shm-dmitry/xray-detector/xray-detector/display_st7735.cpp

#include "display_st7735.h"

#include "Arduino.h"
#include "clock.h"
#include "avr/pgmspace.h"

#define ST_CMD_DELAY 0x80 // special signifier for command lists

#define ST77XX_SWRESET 0x01
#define ST77XX_SLPOUT 0x11
#define ST77XX_MADCTL 0x36
#define ST77XX_INVOFF 0x20
#define ST77XX_COLMOD 0x3A
#define ST77XX_CASET 0x2A
#define ST77XX_RASET 0x2B
#define ST77XX_NORON 0x13
#define ST77XX_DISPON 0x29

#define ST7735_FRMCTR1 0xB1
#define ST7735_FRMCTR2 0xB2
#define ST7735_FRMCTR3 0xB3
#define ST7735_INVCTR 0xB4
#define ST7735_PWCTR1 0xC0
#define ST7735_PWCTR2 0xC1
#define ST7735_PWCTR3 0xC2
#define ST7735_PWCTR4 0xC3
#define ST7735_PWCTR5 0xC4
#define ST7735_VMCTR1 0xC5
#define ST7735_GMCTRP1 0xE0
#define ST7735_GMCTRN1 0xE1

#define ST77XX_MADCTL_MY 0x80
#define ST77XX_MADCTL_MX 0x40
#define ST77XX_MADCTL_MV 0x20
#define ST77XX_MADCTL_RGB 0x00

static const uint8_t PROGMEM DISPLAY_ST7335_COMMAND_LIST1[] = {                       // 7735R init, part 1 (red or green tab)
    15,                             // 15 commands in list:
    ST77XX_SWRESET,   ST_CMD_DELAY, //  1: Software reset, 0 args, w/delay
      150,                          //     150 ms delay
    ST77XX_SLPOUT,    ST_CMD_DELAY, //  2: Out of sleep mode, 0 args, w/delay
      255,                          //     500 ms delay
    ST7735_FRMCTR1, 3,              //  3: Framerate ctrl - normal mode, 3 arg:
      0x01, 0x2C, 0x2D,             //     Rate = fosc/(1x2+40) * (LINE+2C+2D)
    ST7735_FRMCTR2, 3,              //  4: Framerate ctrl - idle mode, 3 args:
      0x01, 0x2C, 0x2D,             //     Rate = fosc/(1x2+40) * (LINE+2C+2D)
    ST7735_FRMCTR3, 6,              //  5: Framerate - partial mode, 6 args:
      0x01, 0x2C, 0x2D,             //     Dot inversion mode
      0x01, 0x2C, 0x2D,             //     Line inversion mode
    ST7735_INVCTR,  1,              //  6: Display inversion ctrl, 1 arg:
      0x07,                         //     No inversion
    ST7735_PWCTR1,  3,              //  7: Power control, 3 args, no delay:
      0xA2,
      0x02,                         //     -4.6V
      0x84,                         //     AUTO mode
    ST7735_PWCTR2,  1,              //  8: Power control, 1 arg, no delay:
      0xC5,                         //     VGH25=2.4C VGSEL=-10 VGH=3 * AVDD
    ST7735_PWCTR3,  2,              //  9: Power control, 2 args, no delay:
      0x0A,                         //     Opamp current small
      0x00,                         //     Boost frequency
    ST7735_PWCTR4,  2,              // 10: Power control, 2 args, no delay:
      0x8A,                         //     BCLK/2,
      0x2A,                         //     opamp current small & medium low
    ST7735_PWCTR5,  2,              // 11: Power control, 2 args, no delay:
      0x8A, 0xEE,
    ST7735_VMCTR1,  1,              // 12: Power control, 1 arg, no delay:
      0x0E,
    ST77XX_INVOFF,  0,              // 13: Don't invert display, no args
    ST77XX_MADCTL,  1,              // 14: Mem access ctl (directions), 1 arg:
      0xC8,                         //     row/col addr, bottom-top refresh
    ST77XX_COLMOD,  1,              // 15: set color mode, 1 arg, no delay:
      0x05 };                       //     16-bit color

static const uint8_t PROGMEM DISPLAY_ST7335_COMMAND_LIST2[] = {                    // 7735R init, part 2 (red tab only)
    2,                              //  2 commands in list:
    ST77XX_CASET,   4,              //  1: Column addr set, 4 args, no delay:
      0x00, 0x00,                   //     XSTART = 0
      0x00, 0x7F,                   //     XEND = 127
    ST77XX_RASET,   4,              //  2: Row addr set, 4 args, no delay:
      0x00, 0x00,                   //     XSTART = 0
      0x00, 0x9F };

static const uint8_t PROGMEM DISPLAY_ST7335_COMMAND_LIST3[] = {                       // 7735R init, part 3 (red or green tab)
    4,                              //  4 commands in list:
    ST7735_GMCTRP1, 16      ,       //  1: Gamma Adjustments (pos. polarity), 16 args + delay:
      0x02, 0x1c, 0x07, 0x12,       //     (Not entirely necessary, but provides
      0x37, 0x32, 0x29, 0x2d,       //      accurate colors)
      0x29, 0x25, 0x2B, 0x39,
      0x00, 0x01, 0x03, 0x10,
    ST7735_GMCTRN1, 16      ,       //  2: Gamma Adjustments (neg. polarity), 16 args + delay:
      0x03, 0x1d, 0x07, 0x06,       //     (Not entirely necessary, but provides
      0x2E, 0x2C, 0x29, 0x2D,       //      accurate colors)
      0x2E, 0x2E, 0x37, 0x3F,
      0x00, 0x00, 0x02, 0x10,
    ST77XX_NORON,     ST_CMD_DELAY, //  3: Normal display on, no args, w/delay
      10,                           //     10 ms delay
    ST77XX_DISPON,    ST_CMD_DELAY, //  4: Main screen turn on, no args w/delay
      100 };                        //     100 ms delay


void display_st7735_run_command_list(const uint8_t *addr);

void display_st7735_init(uint8_t dc) {
  display_spi_init(dc);

  display_st7735_run_command_list(DISPLAY_ST7335_COMMAND_LIST1);
  display_st7735_run_command_list(DISPLAY_ST7335_COMMAND_LIST2);
  display_st7735_run_command_list(DISPLAY_ST7335_COMMAND_LIST3);

  uint8_t madctl = 0xC0;
  display_spi_send_command(ST77XX_MADCTL, &madctl, 1);

  madctl = ST77XX_MADCTL_MX | ST77XX_MADCTL_MY | ST77XX_MADCTL_RGB;
  display_spi_send_command(ST77XX_MADCTL, &madctl, 1);

  madctl = ST77XX_MADCTL_MX | ST77XX_MADCTL_MV | ST77XX_MADCTL_RGB;
  display_spi_send_command(ST77XX_MADCTL, &madctl, 1);
}

void display_st7735_run_command_list(const uint8_t *addr) {

  uint8_t numCommands, cmd, numArgs;
  uint16_t ms;

  numCommands = pgm_read_byte(addr++); // Number of commands to follow
  while (numCommands--) {              // For each command...
    cmd = pgm_read_byte(addr++);       // Read command
    numArgs = pgm_read_byte(addr++);   // Number of args to follow
    ms = numArgs & ST_CMD_DELAY;       // If hibit set, delay follows args
    numArgs &= ~ST_CMD_DELAY;          // Mask out delay bit
    display_spi_send_command_pgm(cmd, addr, numArgs);
    addr += numArgs;

    if (ms) {
      ms = pgm_read_byte(addr++); // Read post-command delay time (ms)
      if (ms == 255)
        ms = 500; // If 255, delay for 500 ms
      clock_delay(ms);
    }
  }
}
