shm-dmitry/xray-detector/xray-detector/gui_page_settings.cpp

#include "gui_page_settings.h"

#include "display.h"
#include "eeprom_control.h"
#include "uv_control.h"
#include "alarm_manager.h"
#include "gui_images.h"
#include "userinput.h"
#include "clock.h"
#include "rad_control.h"

#define SETTINGS_PAGE_UV_FREQ     0
#define SETTINGS_PAGE_UV_DUTY     1
#define SETTINGS_PAGE_UV_ON       2
#define SETTINGS_PAGE_DATE        3
#define SETTINGS_PAGE_TIME        4
#define SETTINGS_PAGE_IMPL2UR     5
#define SETTINGS_PAGE_ALARM_H     6
#define SETTINGS_PAGE_ALRM_L1     7
#define SETTINGS_PAGE_ALRM_L2     8
#define SETTINGS_PAGE_ALRM_NI     9
#define SETTINGS_PAGE_ALRM_OI     10

#define SETTINGS_PAGE_MINVAL  SETTINGS_PAGE_UV_FREQ
#define SETTINGS_PAGE_MAXVAL  SETTINGS_PAGE_ALRM_OI

#define SETTINGS_PAGE_UNCHANGED 0xFF

#define SETTINGS_PAGE_EDIT_DATETIME_UNCHANGED 0
#define SETTINGS_PAGE_EDIT_DATETIME_YEAR      1
#define SETTINGS_PAGE_EDIT_DATETIME_MONTH     2
#define SETTINGS_PAGE_EDIT_DATETIME_DAY       3
#define SETTINGS_PAGE_EDIT_DATETIME_HOUR      4
#define SETTINGS_PAGE_EDIT_DATETIME_MINUTE    5

#define SETTINGS_PAGE_Y_OFFSET 33

uint8_t menu_actual_prev   = SETTINGS_PAGE_MINVAL;
uint8_t menu_actual        = SETTINGS_PAGE_MINVAL;
uint8_t menu_change_value  = SETTINGS_PAGE_UNCHANGED;
bool menu_refreshed        = false;
uint8_t menu_edit_datetime = SETTINGS_PAGE_EDIT_DATETIME_UNCHANGED;

void gui_settings_page_print(uint8_t index, uint8_t value, const char * text);
void gui_settings_page_print_onoff(uint8_t index, bool value);
void gui_settings_page_print_date(uint8_t index);
void gui_settings_page_print_time(uint8_t index);
void gui_settings_page_print_alarm_onimpulse(uint8_t index);

bool gui_settings_page_refresh(uint8_t data) {
  if (!display_is_on()) {
    return false;
  }

  display_set_cursor(0, SETTINGS_PAGE_Y_OFFSET);
  display_set_textcolor(DISPLAY_WHITE);
  display_set_textsize(2);

  if (data) {
    if (data == USERINPUT_MOVE_LEFT) {
      menu_actual = SETTINGS_PAGE_MAXVAL;
    } else {
      menu_actual = SETTINGS_PAGE_MINVAL;
    }

    display_println("  UV freq: ");
    display_println("  UV freq: ");
    display_println("  UV: ");
    display_println("  Date: ");
    display_println("  Time: ");
    display_println("  Impl/uR: ");
    display_println(" Alarms:");
    display_println("  Level1: ");
    display_println("  Level2: ");
    display_println("  No Impuls: ");
    display_println("  On Each: ");
  }

  if (menu_actual_prev != menu_actual || data) {
    display_draw_bitmap(6, SETTINGS_PAGE_Y_OFFSET + 16 * menu_actual_prev + 5, IMG_ARROW, IMG_ARROW_W, IMG_ARROW_H, DISPLAY_BLACK);
    display_draw_bitmap(6, SETTINGS_PAGE_Y_OFFSET + 16 * menu_actual + 5, IMG_ARROW, IMG_ARROW_W, IMG_ARROW_H, DISPLAY_YELLOW);
    menu_actual_prev = menu_actual;
  }

  if (data || !menu_refreshed) {
    gui_settings_page_print(SETTINGS_PAGE_UV_FREQ, eeprom_control_get_freq(), "KHz");
    gui_settings_page_print(SETTINGS_PAGE_UV_DUTY, eeprom_control_get_duty(), "%");
    gui_settings_page_print_onoff(SETTINGS_PAGE_UV_ON, uv_control_is_on()); 
    gui_settings_page_print(SETTINGS_PAGE_ALRM_L1, alarm_manager_getlevel(1), "uR"); 
    gui_settings_page_print(SETTINGS_PAGE_ALRM_L2, alarm_manager_getlevel(2), "mR"); 
    gui_settings_page_print(SETTINGS_PAGE_ALRM_NI, alarm_manager_getlevel(ALARM_MANAGER_NI_LEVEL), "sec"); 
    gui_settings_page_print_alarm_onimpulse(SETTINGS_PAGE_ALRM_OI);
    gui_settings_page_print_date(SETTINGS_PAGE_DATE);
    gui_settings_page_print_time(SETTINGS_PAGE_TIME);
    gui_settings_page_print(SETTINGS_PAGE_IMPL2UR, eeprom_control_get_impl_per_ur(), NULL); // possible overflow here!
  }

  menu_refreshed = true;

  return false;
}

void gui_settings_page_print_onimpulse_type(uint8_t value) {
  if (value == ALARM_MANAGER_ONIMPULSE_VOICE_NONE) {
    display_prints("none");
  } else if (value == ALARM_MANAGER_ONIMPULSE_VOICE_VIBRO) {
    display_prints("vibro");
  } else if (value == ALARM_MANAGER_ONIMPULSE_VOICE_VOICE) {
    display_prints("voice");
  } else if (value == ALARM_MANAGER_ONIMPULSE_VOICE_VIBRO_AND_VOICE) {
    display_prints("vibro&sound");
  }
}

void gui_settings_page_print_alarm_onimpulse(uint8_t index) {
  display_set_cursor(160, SETTINGS_PAGE_Y_OFFSET + 16 * index);
  display_fill_rect(display_get_cursor_x(), display_get_cursor_y(), 160, 16, DISPLAY_BLACK);

  if (menu_actual == index && menu_change_value != SETTINGS_PAGE_UNCHANGED) {
    display_set_textcolor(DISPLAY_YELLOW);
    display_prints("<");
    gui_settings_page_print_onimpulse_type(menu_change_value);
    display_prints(">");
  } else {
    display_set_textcolor(DISPLAY_WHITE);
    gui_settings_page_print_onimpulse_type(eeprom_control_get_onimpulse_voice());
  }
}

void gui_settings_page_print(uint8_t index, uint8_t value, const char * text) {
  display_set_cursor(160, SETTINGS_PAGE_Y_OFFSET + 16 * index);
  display_fill_rect(display_get_cursor_x(), display_get_cursor_y(), 160, 16, DISPLAY_BLACK);

  if (menu_actual == index && menu_change_value != SETTINGS_PAGE_UNCHANGED) {
    display_set_textcolor(DISPLAY_YELLOW);
    display_prints("<");
    display_print8(menu_change_value);
    if (text) {
      display_prints(" ");
      display_prints(text);
    }
    display_prints(">");
  } else {
    display_set_textcolor(DISPLAY_WHITE);
    display_print8(value);
    if (text) {
      display_prints(" ");
      display_prints(text);
    }
  }
}

void gui_settings_page_print_date(uint8_t index) {
  display_set_cursor(160, SETTINGS_PAGE_Y_OFFSET + 16 * index);
  display_fill_rect(display_get_cursor_x(), display_get_cursor_y(), 160, 16, DISPLAY_BLACK);
  
  if (menu_actual == index && menu_change_value != SETTINGS_PAGE_UNCHANGED) {
    if (menu_edit_datetime == SETTINGS_PAGE_EDIT_DATETIME_YEAR) {
      display_set_textcolor(DISPLAY_YELLOW);
      display_prints("<20");
      display_print8(menu_change_value);
      display_prints(">");
    } else {
      display_set_textcolor(DISPLAY_WHITE);
      display_print16(clock_get_component(CLOCK_COMPONENT_YEAR));
    }
    display_set_textcolor(DISPLAY_WHITE);
    display_prints("-");
    if (menu_edit_datetime == SETTINGS_PAGE_EDIT_DATETIME_MONTH) {
      display_set_textcolor(DISPLAY_YELLOW);
      display_prints("<");
      display_print8(menu_change_value);
      display_prints(">");
    } else {
      display_set_textcolor(DISPLAY_WHITE);
      uint8_t temp = clock_get_component(CLOCK_COMPONENT_MONTH);
      if (temp <= 9) {
        display_prints("0");
      }
      display_print8(temp);
    }
    display_set_textcolor(DISPLAY_WHITE);
    display_prints("-");
    if (menu_edit_datetime == SETTINGS_PAGE_EDIT_DATETIME_DAY) {
      display_set_textcolor(DISPLAY_YELLOW);
      display_prints("<");
      display_print8(menu_change_value);
      display_prints(">");
    } else {
      display_set_textcolor(DISPLAY_WHITE);
      uint8_t temp = clock_get_component(CLOCK_COMPONENT_DAY);
      if (temp <= 9) {
        display_prints("0");
      }
      display_print8(temp);
    }
  } else {
    display_set_textcolor(DISPLAY_WHITE);
    display_print16(clock_get_component(CLOCK_COMPONENT_YEAR));
    uint8_t temp = clock_get_component(CLOCK_COMPONENT_MONTH);
    if (temp <= 9) {
      display_prints("-0");
    } else {
      display_prints("-");
    }
    display_print8(temp);
    temp = clock_get_component(CLOCK_COMPONENT_DAY);
    if (temp <= 9) {
      display_prints("-0");
    } else {
      display_prints("-");
    }
    display_print8(temp);
  }
}

void gui_settings_page_print_time(uint8_t index) {
  display_set_cursor(160, SETTINGS_PAGE_Y_OFFSET + 16 * index);
  display_fill_rect(display_get_cursor_x(), display_get_cursor_y(), 160, 16, DISPLAY_BLACK);
  
  if (menu_actual == index && menu_change_value != SETTINGS_PAGE_UNCHANGED) {
    if (menu_edit_datetime == SETTINGS_PAGE_EDIT_DATETIME_HOUR) {
      display_set_textcolor(DISPLAY_YELLOW);
      display_prints("<");
      display_print8(menu_change_value);
      display_prints(">");
    } else {
      display_set_textcolor(DISPLAY_WHITE);
      uint8_t temp = clock_get_component(CLOCK_COMPONENT_HOUR);
      if (temp <= 9) {
        display_prints("0");
      }
      display_print8(temp);
    }
    display_set_textcolor(DISPLAY_WHITE);
    display_prints(":");
    if (menu_edit_datetime == SETTINGS_PAGE_EDIT_DATETIME_MINUTE) {
      display_set_textcolor(DISPLAY_YELLOW);
      display_prints("<");
      display_print8(menu_change_value);
      display_prints(">");
    } else {
      display_set_textcolor(DISPLAY_WHITE);
      uint8_t temp = clock_get_component(CLOCK_COMPONENT_MINUTE);
      if (temp <= 9) {
        display_prints("0");
      }
      display_print8(temp);
    }
  } else {
    display_set_textcolor(DISPLAY_WHITE);
    uint8_t temp = clock_get_component(CLOCK_COMPONENT_HOUR);
    if (temp <= 9) {
      display_prints("0");
    }
    display_print8(temp);
    temp = clock_get_component(CLOCK_COMPONENT_MINUTE);
    if (temp <= 9) {
      display_prints(":0");
    } else {
      display_prints(":");
    }
    display_print8(temp);
  }
}

void gui_settings_page_print_onoff(uint8_t index, bool value) {
  display_set_cursor(160, SETTINGS_PAGE_Y_OFFSET + 16 * index);
  display_fill_rect(display_get_cursor_x(), display_get_cursor_y(), 160, 16, DISPLAY_BLACK);
  
  if (menu_actual == index && menu_change_value != SETTINGS_PAGE_UNCHANGED) {
    display_set_textcolor(DISPLAY_YELLOW);
    display_prints("<");
    display_prints(value ? "ON" : "OFF");
    display_prints(">");
  } else {
    display_set_textcolor(DISPLAY_WHITE);
    display_prints(value ? "ON" : "OFF");
  }
}

bool gui_settings_page_on_left(bool fast) {
  if (menu_actual == SETTINGS_PAGE_UV_FREQ && menu_change_value != SETTINGS_PAGE_UNCHANGED) {
    menu_change_value -= fast ? 3 : 1;
    if (menu_change_value < 60) {
      menu_change_value = 60;
    }

    uv_control_change_pwm_with_testrun_freq(menu_change_value, eeprom_control_get_duty());

    menu_refreshed = false;
  } else if (menu_actual == SETTINGS_PAGE_UV_DUTY && menu_change_value != SETTINGS_PAGE_UNCHANGED) {
    uint8_t delta = fast ? 3 : 1;
    if (menu_change_value < delta) {
      menu_change_value = 1;
    } else {
      menu_change_value -= delta;
    }

    uv_control_change_pwm_with_testrun_freq(eeprom_control_get_freq(), menu_change_value);

    menu_refreshed = false;
  } else if (menu_actual == SETTINGS_PAGE_UV_ON && menu_change_value != SETTINGS_PAGE_UNCHANGED) {
    if (uv_control_is_on()) {
      uv_control_disable_pwm();
    } else {
      uv_control_enable_pwm();
    }

    menu_refreshed = false;
  } else if ((menu_actual == SETTINGS_PAGE_ALRM_L1 || menu_actual == SETTINGS_PAGE_ALRM_L2 || menu_actual == SETTINGS_PAGE_ALRM_NI || menu_actual == SETTINGS_PAGE_IMPL2UR) && menu_change_value != SETTINGS_PAGE_UNCHANGED) {
    uint8_t delta = fast ? 10 : 1;
    if (menu_change_value < delta) {
      menu_change_value = 1;
    } else {
      menu_change_value -= delta;
    }

    menu_refreshed = false;
  } else if (menu_actual == SETTINGS_PAGE_ALRM_OI && menu_change_value != SETTINGS_PAGE_UNCHANGED) {
    if (menu_change_value > 0x00) {
      menu_change_value--;
    }
    menu_refreshed = false;
  } else if (menu_actual == SETTINGS_PAGE_DATE && menu_change_value != SETTINGS_PAGE_UNCHANGED) {
    uint8_t delta = 0;
    if (menu_edit_datetime == SETTINGS_PAGE_EDIT_DATETIME_DAY) {
      delta = fast ? 3 : 1;
    } else {
      delta = 1;
    }

    if (menu_change_value <= delta) {
      menu_change_value = 1;
    } else {
      menu_change_value -= delta;
    }

    menu_refreshed = false;
  } else if (menu_actual == SETTINGS_PAGE_TIME && menu_change_value != SETTINGS_PAGE_UNCHANGED) {
    uint8_t delta = fast ? 5 : 1;

    if (menu_change_value <= delta) {
      menu_change_value = 0;
    } else {
      menu_change_value -= delta;
    }

    menu_refreshed = false;
  } else {
    if (menu_actual == SETTINGS_PAGE_MINVAL) {
      return false;
    } else {
      menu_actual--;
      if (menu_actual == SETTINGS_PAGE_ALARM_H) {
        menu_actual--;
      }
    }
  }
  
  return true;
}

bool gui_settings_page_on_right(bool fast) {
  if (menu_actual == SETTINGS_PAGE_UV_FREQ && menu_change_value != SETTINGS_PAGE_UNCHANGED) {
    menu_change_value += fast ? 3 : 1;
    if (menu_change_value > 130) {
      menu_change_value = 130;
    }

    uv_control_change_pwm_with_testrun_freq(menu_change_value, eeprom_control_get_duty());

    menu_refreshed = false;
  } else if (menu_actual == SETTINGS_PAGE_UV_DUTY && menu_change_value != SETTINGS_PAGE_UNCHANGED) {
    menu_change_value += fast ? 3 : 1;
    if (menu_change_value > 30) {
      menu_change_value = 30;
    }

    uv_control_change_pwm_with_testrun_freq(eeprom_control_get_freq(), menu_change_value);

    menu_refreshed = false;
  } else if (menu_actual == SETTINGS_PAGE_UV_ON && menu_change_value != SETTINGS_PAGE_UNCHANGED) {
    if (uv_control_is_on()) {
      uv_control_disable_pwm();
    } else {
      uv_control_enable_pwm();
    }

    menu_refreshed = false;
  } else if ((menu_actual == SETTINGS_PAGE_ALRM_L1 || menu_actual == SETTINGS_PAGE_ALRM_L2 || menu_actual == SETTINGS_PAGE_ALRM_NI || menu_actual == SETTINGS_PAGE_IMPL2UR) && menu_change_value != SETTINGS_PAGE_UNCHANGED) {
    menu_change_value += fast ? 10 : 1;
    if (menu_change_value > 240) {
      menu_change_value = 240;
    }

    menu_refreshed = false;
  } else if (menu_actual == SETTINGS_PAGE_ALRM_OI && menu_change_value != SETTINGS_PAGE_UNCHANGED) {
    if (menu_change_value < ALARM_MANAGER_ONIMPULSE_VOICE_MAXVALUE) {
      menu_change_value++;
    }
    menu_refreshed = false;
  } else if (menu_actual == SETTINGS_PAGE_DATE && menu_change_value != SETTINGS_PAGE_UNCHANGED) {
    uint8_t delta = 0;
    if (menu_edit_datetime == SETTINGS_PAGE_EDIT_DATETIME_DAY) {
      delta = fast ? 3 : 1;
    } else {
      delta = 1;
    }

    menu_change_value += delta;

    if (menu_edit_datetime == SETTINGS_PAGE_EDIT_DATETIME_MONTH && menu_change_value > 12) {
      menu_change_value = 12;
    } else if (menu_edit_datetime == SETTINGS_PAGE_EDIT_DATETIME_DAY && menu_change_value > clock_days_in_month()) {
      menu_change_value = clock_days_in_month();
    }

    menu_refreshed = false;
  } else if (menu_actual == SETTINGS_PAGE_TIME && menu_change_value != SETTINGS_PAGE_UNCHANGED) {
    menu_change_value += fast ? 5 : 1;

    if (menu_edit_datetime == SETTINGS_PAGE_EDIT_DATETIME_HOUR && menu_change_value >= 23) {
      menu_change_value = 23;
    } else if (menu_edit_datetime == SETTINGS_PAGE_EDIT_DATETIME_MINUTE && menu_change_value >= 59) {
      menu_change_value = 59;
    } 

    menu_refreshed = false;
  } else {
    if (menu_actual == SETTINGS_PAGE_MAXVAL) {
      return false;
    } else {
      menu_actual++;
      if (menu_actual == SETTINGS_PAGE_ALARM_H) {
        menu_actual++;
      }
    }
  }
  
  return true;
}

bool gui_settings_page_on_move(uint8_t data) {
  if (data == USERINPUT_MOVE_LEFT || data == USERINPUT_MOVE_LEFTFAST) {
    return gui_settings_page_on_left(data == USERINPUT_MOVE_LEFTFAST);
  } else {
    return gui_settings_page_on_right(data == USERINPUT_MOVE_RIGHTFAST);
  }
}

bool gui_settings_page_on_click(uint8_t) {
  if (menu_actual == SETTINGS_PAGE_UV_FREQ) {
    if (menu_change_value == SETTINGS_PAGE_UNCHANGED) {
      menu_change_value = eeprom_control_get_freq();
    } else {
      eeprom_control_save_freq(menu_change_value);
      menu_change_value = SETTINGS_PAGE_UNCHANGED;
    }
  } else if (menu_actual == SETTINGS_PAGE_UV_DUTY) {
    if (menu_change_value == SETTINGS_PAGE_UNCHANGED) {
      menu_change_value = eeprom_control_get_duty();
    } else {
      eeprom_control_save_duty(menu_change_value);
      menu_change_value = SETTINGS_PAGE_UNCHANGED;
    }
  } else if (menu_actual == SETTINGS_PAGE_UV_ON) {
    menu_change_value = menu_change_value == SETTINGS_PAGE_UNCHANGED ? 1 : SETTINGS_PAGE_UNCHANGED;
  } else if (menu_actual == SETTINGS_PAGE_ALRM_L1 || menu_actual == SETTINGS_PAGE_ALRM_L2) {
    if (menu_change_value == SETTINGS_PAGE_UNCHANGED) {
      menu_change_value = alarm_manager_getlevel(menu_actual == SETTINGS_PAGE_ALRM_L1 ? 1 : 2);
    } else {
      if (menu_actual == SETTINGS_PAGE_ALRM_L1) {
        eeprom_control_save_alarm_levels(menu_change_value, alarm_manager_getlevel(2));
      } else {
        eeprom_control_save_alarm_levels(alarm_manager_getlevel(1), menu_change_value);
      }
      alarm_manager_refresh_levels();
      menu_change_value = SETTINGS_PAGE_UNCHANGED;
    }
  } else if (menu_actual == SETTINGS_PAGE_ALRM_NI) {
    if (menu_change_value == SETTINGS_PAGE_UNCHANGED) {
      menu_change_value = alarm_manager_getlevel(ALARM_MANAGER_NI_LEVEL);
    } else {
      eeprom_control_set_noimpulse_seconds(menu_change_value);
      alarm_manager_refresh_levels();
      menu_change_value = SETTINGS_PAGE_UNCHANGED;
    }
  } else if (menu_actual == SETTINGS_PAGE_ALRM_OI) {
    if (menu_change_value == SETTINGS_PAGE_UNCHANGED) {
      menu_change_value = eeprom_control_get_onimpulse_voice();
    } else {
      eeprom_control_save_onimpulse_voice(menu_change_value);
      alarm_manager_refresh_levels();
      menu_change_value = SETTINGS_PAGE_UNCHANGED;
    }
  } else if (menu_actual == SETTINGS_PAGE_IMPL2UR) {
    if (menu_change_value == SETTINGS_PAGE_UNCHANGED) {
      menu_change_value = eeprom_control_get_impl_per_ur();
    } else {
      eeprom_control_save_impl_per_ur(menu_change_value);
      rad_control_refresh_impl_per_ur();
      menu_change_value = SETTINGS_PAGE_UNCHANGED;
    }
  } else if (menu_actual == SETTINGS_PAGE_DATE) {
    if (menu_change_value == SETTINGS_PAGE_UNCHANGED) {
      menu_edit_datetime = SETTINGS_PAGE_EDIT_DATETIME_YEAR;
      menu_change_value = clock_get_component(CLOCK_COMPONENT_YEAR) - 2000;
    } else if (menu_edit_datetime == SETTINGS_PAGE_EDIT_DATETIME_YEAR) {
      clock_set_component(CLOCK_COMPONENT_YEAR, menu_change_value + 2000);
      menu_edit_datetime = SETTINGS_PAGE_EDIT_DATETIME_MONTH;
      menu_change_value = clock_get_component(CLOCK_COMPONENT_MONTH);
    } else if (menu_edit_datetime == SETTINGS_PAGE_EDIT_DATETIME_MONTH) {
      clock_set_component(CLOCK_COMPONENT_MONTH, menu_change_value);
      menu_edit_datetime = SETTINGS_PAGE_EDIT_DATETIME_DAY;
      menu_change_value = clock_get_component(CLOCK_COMPONENT_DAY);
    } else {
      clock_set_component(CLOCK_COMPONENT_DAY, menu_change_value);
      menu_edit_datetime = SETTINGS_PAGE_EDIT_DATETIME_UNCHANGED;
      menu_change_value = SETTINGS_PAGE_UNCHANGED;
    }
  } else if (menu_actual == SETTINGS_PAGE_TIME) {
    if (menu_change_value == SETTINGS_PAGE_UNCHANGED) {
      menu_edit_datetime = SETTINGS_PAGE_EDIT_DATETIME_HOUR;
      menu_change_value = clock_get_component(CLOCK_COMPONENT_HOUR);
    } else if (menu_edit_datetime == SETTINGS_PAGE_EDIT_DATETIME_HOUR) {
      clock_set_component(CLOCK_COMPONENT_HOUR, menu_change_value);
      menu_edit_datetime = SETTINGS_PAGE_EDIT_DATETIME_MINUTE;
      menu_change_value = clock_get_component(CLOCK_COMPONENT_MINUTE);
    } else {
      clock_set_component(CLOCK_COMPONENT_MINUTE, menu_change_value);
      menu_edit_datetime = SETTINGS_PAGE_EDIT_DATETIME_UNCHANGED;
      menu_change_value = SETTINGS_PAGE_UNCHANGED;
    }
  }

  menu_refreshed = false;
  
  return true;
}

bool gui_settings_page_onwakeup(uint8_t) {
  menu_actual_prev   = SETTINGS_PAGE_MINVAL;
  menu_actual        = SETTINGS_PAGE_MINVAL;
  menu_change_value  = SETTINGS_PAGE_UNCHANGED;
  menu_refreshed     = false;
  menu_edit_datetime = SETTINGS_PAGE_EDIT_DATETIME_UNCHANGED;

  return true;
}
