shm-dmitry/xray-detector/xray-src-v3/xray-v3-ui/user_input.cpp

#include "user_input.h"

#include "Arduino.h"

#define USER_INPUT_SLEEP_DELAY (20*1000L)

volatile boolean user_input_button_pressed = false;
volatile uint32_t user_input_next_allow_sleep = 0; 

void isrcall__on_user_input();

void user_input_init() {
  pinMode(PIN_PA5, INPUT);
  attachInterrupt(digitalPinToInterrupt(PIN_PA5), isrcall__on_user_input, FALLING);

  user_input_next_allow_sleep = millis() + USER_INPUT_SLEEP_DELAY;
}

void isrcall__on_user_input() {
  user_input_button_pressed = true;
  user_input_next_allow_sleep = millis() + USER_INPUT_SLEEP_DELAY;
}

bool user_input_can_sleep() {
  return user_input_next_allow_sleep > millis();
}
