shm-dmitry/xray-detector/xray-src-v3/xray-v3-ui/display_st7789.h

#pragma once

/**
This code based on projects:
- https://github.com/Tehnoves/Adafruit_st7789
- https://github.com/adafruit/Adafruit_ILI9341
- https://github.com/adafruit/Adafruit-GFX-Library
*/

#include "stdint.h"

void display_st7789_init(uint8_t dc);
