shm-dmitry/xray-detector/xray-detector/gui_images.h

#ifndef GUI_IMAGES_H_
#define GUI_IMAGES_H_

#include "Arduino.h"

#define IMG_XRAY_SMALL_W  16
#define IMG_XRAY_SMALL_H  16
static const uint8_t PROGMEM IMG_XRAY_SMALL[] = {   
  0x03, 0xc0, 0x07, 0xe0, 0x07, 0xe0, 0x07, 0xe0, 0x03, 0xc0, 0x03, 0xc0,
  0x03, 0xc0, 0x01, 0x80, 0x07, 0xe0, 0x1f, 0xf8, 0x7e, 0x7e, 0x7c, 0x3e,
  0xfc, 0x3f, 0xf8, 0x1f, 0xf8, 0x1f, 0xe0, 0x07};

#define IMG_XRAY_SMALL_BETTA_W  16
#define IMG_XRAY_SMALL_BETTA_H  16
static const uint8_t PROGMEM IMG_XRAY_SMALL_BETTA[] = {
  0x06, 0x00, 0x0f, 0x00, 0x0f, 0x00, 0x0f, 0x00, 0x06, 0x00, 0x06, 0x00,
  0x0f, 0x0f, 0x3f, 0xc9, 0x79, 0xe9, 0x79, 0xef, 0x79, 0xe9, 0x30, 0xc9,
  0x00, 0x0f, 0x00, 0x18, 0x00, 0x30, 0x00, 0x60};

#define IMG_FLASH_W  16
#define IMG_FLASH_H  16
static const uint8_t PROGMEM IMG_FLASH[] = {
  0x00, 0x00, 0x00, 0x03, 0x00, 0x07, 0x00, 0x0f, 0x00, 0x1f, 0xff, 0xff,
  0xff, 0xff, 0xf0, 0xff, 0xf0, 0xff, 0xff, 0xff, 0xff, 0xff, 0x00, 0x1f,
  0x00, 0x0f, 0x00, 0x07, 0x00, 0x03, 0x00, 0x00};

#define IMG_BAT_W  16
#define IMG_BAT_H  16
static const uint8_t PROGMEM IMG_BAT[] = {
  0x00, 0x00, 0x00, 0x00, 0x00, 0x00, 0x00, 0x00, 0x00, 0x00, 0xff, 0xfc,
  0xff, 0x84, 0xff, 0x87, 0xff, 0x87, 0xff, 0x84, 0xff, 0xfc, 0x00, 0x00,
  0x00, 0x00, 0x00, 0x00, 0x00, 0x00, 0x00, 0x00};

#define IMG_SETTINGS_W  16
#define IMG_SETTINGS_H  16
static const uint8_t PROGMEM IMG_SETTINGS[] = {
  0x00, 0x00, 0x01, 0x80, 0x31, 0x8c, 0x3b, 0xdc, 0x1e, 0x78, 0x0c, 0x30,
  0x18, 0x18, 0x71, 0x8e, 0x71, 0x8e, 0x18, 0x18, 0x0c, 0x30, 0x1e, 0x78,
  0x3b, 0xdc, 0x31, 0x8c, 0x01, 0x80, 0x00, 0x00};

#define IMG_ARROW_W  8
#define IMG_ARROW_H  8
static const uint8_t PROGMEM IMG_ARROW[] = {0x08, 0x0c, 0x0e, 0xff, 0xff, 0x0e, 0x0c, 0x08};

#define IMG_CIRCLE_W  8
#define IMG_CIRCLE_H  8
static const uint8_t PROGMEM IMG_CIRCLE[] = {0x3c, 0x7e, 0xe7, 0xc3, 0xc3, 0xe7, 0x7e, 0x3c};

#define IMG_CIRCLE_LOW_W  8
#define IMG_CIRCLE_LOW_H  8
static const uint8_t PROGMEM IMG_CIRCLE_LOW[] = {0x00, 0x00, 0x18, 0x3c, 0x3c, 0x18, 0x00, 0x00};

#define IMG_TRIANGLE_W  8
#define IMG_TRIANGLE_H  8
static const uint8_t PROGMEM IMG_TRIANGLE[] = {0x03, 0x0f, 0x3f, 0xff, 0xff, 0x3f, 0x0f, 0x03};


struct t_icon {
  uint8_t w;
  uint8_t h;
  const uint8_t * img;
};

static const t_icon IMG_ICONS[5] = {
  {.w = IMG_XRAY_SMALL_W,       .h = IMG_XRAY_SMALL_H,       .img = IMG_XRAY_SMALL},
  {.w = IMG_XRAY_SMALL_BETTA_W, .h = IMG_XRAY_SMALL_BETTA_H, .img = IMG_XRAY_SMALL_BETTA},
  {.w = IMG_FLASH_W,            .h = IMG_FLASH_H,            .img = IMG_FLASH},
  {.w = IMG_BAT_W,              .h = IMG_BAT_H,              .img = IMG_BAT},
  {.w = IMG_SETTINGS_W,         .h = IMG_SETTINGS_H,         .img = IMG_SETTINGS},
};

#endif /* GUI_IMAGES_H_ */
