shm-dmitry/xray-detector/xray-detector/gui_page_bat.h

#ifndef GUI_PAGE_BAT_H_
#define GUI_PAGE_BAT_H_

#include "stdbool.h"
#include "stdint.h"

bool gui_bat_page_refresh(uint8_t data);
bool gui_bat_page_onwakeup(uint8_t data);

#endif /* GUI_PAGE_BAT_H_ */
