shm-dmitry/xray-detector/xray-detector/gui_page_rad_betta.h

#ifndef GUI_PAGE_RAD_BETTA_H_
#define GUI_PAGE_RAD_BETTA_H_

#include "stdbool.h"
#include "stdint.h"

bool gui_rad_page_betta_refresh(uint8_t data);
bool gui_rad_page_betta_onclick(uint8_t data);
bool gui_rad_page_betta_onwakeup(uint8_t data);

#endif /* GUI_PAGE_RAD_BETTA_H_ */
