shm-dmitry/xray-detector/xray-detector/gui_page_borders.h

#ifndef GUI_PAGE_BORDERS_H_
#define GUI_PAGE_BORDERS_H_

#include "stdint.h"

void gui_borders_refresh(uint8_t currentpage, uint8_t pagescount);
void gui_borders_onwakeup();

#endif /* GUI_PAGE_BORDERS_H_ */
