shm-dmitry/xray-detector/xray-detector/gui_page_rad.h

#ifndef GUI_PAGE_RAD_H_
#define GUI_PAGE_RAD_H_

#include "stdbool.h"
#include "stdint.h"

bool gui_rad_page_refresh(uint8_t data);
bool gui_rad_page_onclick(uint8_t data);
bool gui_rad_page_onwakeup(uint8_t data);

#endif /* GUI_PAGE_RAD_H_ */
